emard/esp32thermohygro/pcb/thermohygro.kicad_sch

## KiCad design pcb/thermohygro.kicad_sch (2026-09-04)

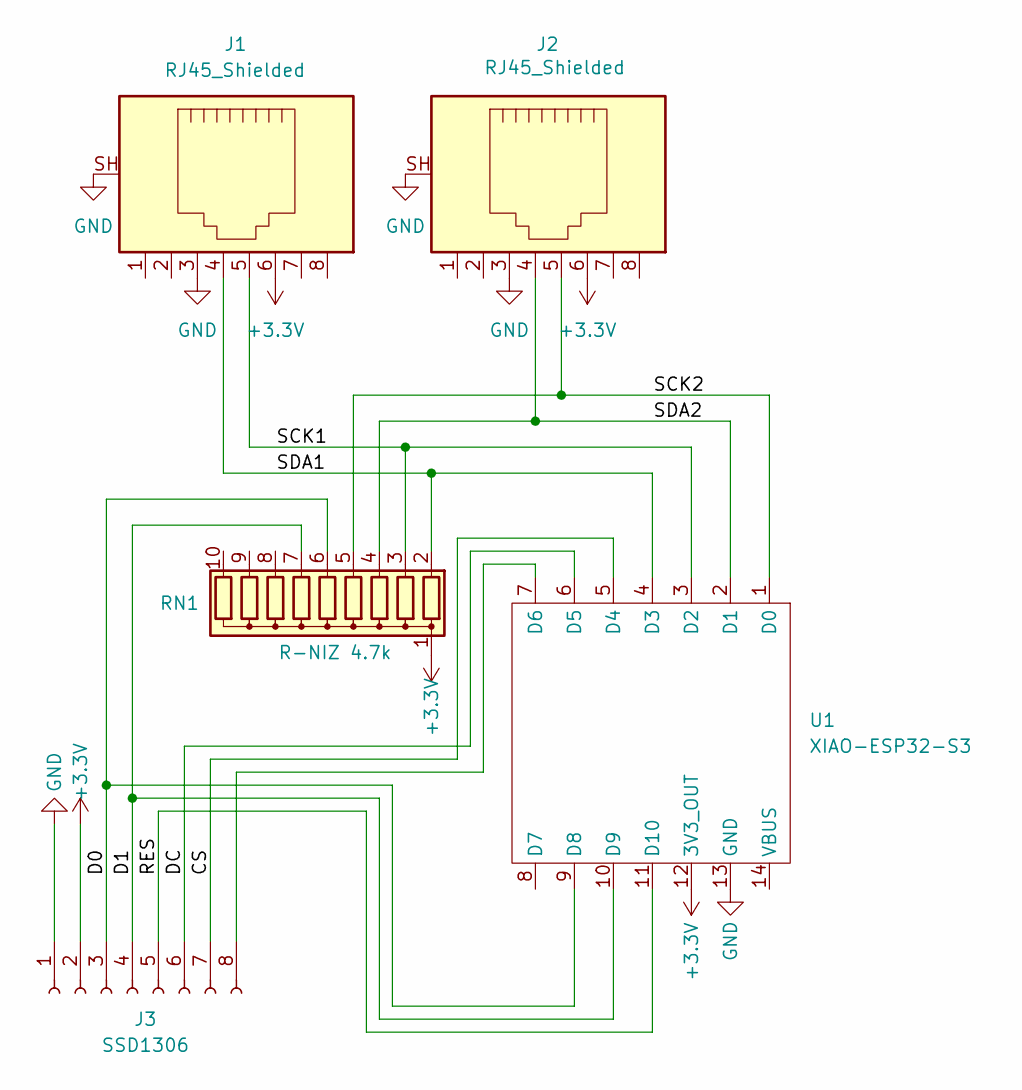
[picture p2: schematic thermohygro.kicad_sch]

Parts:
J1, J2: RJ45_Shielded; RJ45_HALO_HFJ11-x2450HRL_Horizontal_closer
J3: SSD1306; PinSocket_1x08_P2.54mm_Vertical
RN1: R-NIZ 4.7k; R_Array_SIP10
U1: XIAO-ESP32-S3; XIAO-ESP32-S3-DIP

Connections:
+3.3V: J1.6, J2.6, J3.2, RN1.1 (common), U1.12 (3V3_OUT)
CS: J3.7, U1.5 (D4)
D0: J3.3, RN1.6 (R5), U1.9 (D8)
D1: J3.4, RN1.7 (R6), U1.10 (D9)
DC: J3.6, U1.6 (D5)
GND: J1.3, J1.SH, J2.3, J2.SH, J3.1, U1.13 (GND)
unnamed: J3.8, U1.7 (D6)
RES: J3.5, U1.11 (D10)
SCK1: J1.5, RN1.3 (R2), U1.3 (D2)
SCK2: J2.5, RN1.5 (R4), U1.1 (D0)
SDA1: J1.4, RN1.2 (R1), U1.4 (D3)
SDA2: J2.4, RN1.4 (R3), U1.2 (D1)
