emard/esp32thermohygro/micropython/main.py

print("ctrl-c ctrl-dccc")
print("from pye import pye")
print('pye("thwificfg.py")')
print("ctrl-s ctrl-q shift-arrows ctrl-c ctrl-v ctrl-e")
#import thmini
import thweb
#from pye import pye # don't always import to save memory
