emard/esp32thermohygro/micropython/thlogcfg.py

# log basis 1:yearly 2:monthly 3:daily 4:hourly 5:minutely
basis=3
# when to write log
# hours are in UTC (GMT) time zone
# comma separated list of integer sub-basis months/days/hours/minutes/econds
events=()
